PongAlmighty/Arena-Timer-Firmware-Standalone/include/WebServer.h

/**
 * Web Server - HTTP server, web interface, and API for Arena Timer
 * Handles web UI, RESTful API endpoints, and network communications
 */

#pragma once

#include <Ethernet_Generic.hpp>
#include <TimerDisplay.h>

// Forward declaration
class WebSocketClient;

namespace WebServer {
// Pin definitions for W5500
extern const int CS;
extern const int SCK;
extern const int MOSI;
extern const int MISO;

/// @brief Initialize the Ethernet connection with static IP
/// @param mac MAC address (6 bytes)
/// @param ip IP address (4 bytes)
/// @return true if successful, false otherwise
bool init(uint8_t mac[6], uint8_t ip[4]);

/// @brief Initialize mDNS responder for hostname resolution
/// @param hostname Hostname (without .local suffix)
/// @return true if successful, false otherwise
bool initMDNS(const char *hostname);

/// @brief Update mDNS responder (call in loop)
void updateMDNS();

/// @brief Start the web server on specified port
/// @param port Port number (default 80)
void startWebServer(uint16_t port = 80);

/// @brief Handle incoming client connections (call in loop)
/// @param timerDisplay Reference to the TimerDisplay object to control
void handleClient(TimerDisplay &timerDisplay);

/// @brief Set the WebSocket client instance for API access
/// @param wsClient Pointer to WebSocketClient instance
void setWebSocketClient(WebSocketClient *wsClient);

/// @brief Get the current Ethernet server
EthernetServer &getServer();

/// @brief Load settings from filesystem
/// @param timerDisplay Reference to the TimerDisplay object to apply settings
/// to
/// @return true if successful, false otherwise
bool loadSettings(TimerDisplay &timerDisplay);

/// @brief Save settings to filesystem
/// @param timerDisplay Reference to the TimerDisplay object to save settings
/// from
/// @return true if successful, false otherwise
bool saveSettings(TimerDisplay &timerDisplay);

/// @brief Get the IP address as a string
/// @return IP address string (e.g., "192.168.1.100")
String getIPAddressString();
} // namespace WebServer
